RetroLoft/RadioFloppy/main/oled_font.h

/*
 * Classic 5x7 bitmap font, ASCII 0x20..0x7E. One byte per column, bit 0 =
 * top row (the SSD1306 page layout). Characters are drawn 6 pixels apart.
 */
#pragma once

#include <stdint.h>

#define OLED_FONT_FIRST     0x20
#define OLED_FONT_LAST      0x7e
#define OLED_FONT_WIDTH     5
#define OLED_FONT_HEIGHT    7

static const uint8_t oled_font5x7[][OLED_FONT_WIDTH] = {
    { 0x00, 0x00, 0x00, 0x00, 0x00 }, /* ' ' */  { 0x00, 0x00, 0x5f, 0x00, 0x00 }, /* ! */
    { 0x00, 0x07, 0x00, 0x07, 0x00 }, /* " */    { 0x14, 0x7f, 0x14, 0x7f, 0x14 }, /* # */
    { 0x24, 0x2a, 0x7f, 0x2a, 0x12 }, /* $ */    { 0x23, 0x13, 0x08, 0x64, 0x62 }, /* % */
    { 0x36, 0x49, 0x55, 0x22, 0x50 }, /* & */    { 0x00, 0x05, 0x03, 0x00, 0x00 }, /* ' */
    { 0x00, 0x1c, 0x22, 0x41, 0x00 }, /* ( */    { 0x00, 0x41, 0x22, 0x1c, 0x00 }, /* ) */
    { 0x08, 0x2a, 0x1c, 0x2a, 0x08 }, /* * */    { 0x08, 0x08, 0x3e, 0x08, 0x08 }, /* + */
    { 0x00, 0x50, 0x30, 0x00, 0x00 }, /* , */    { 0x08, 0x08, 0x08, 0x08, 0x08 }, /* - */
    { 0x00, 0x60, 0x60, 0x00, 0x00 }, /* . */    { 0x20, 0x10, 0x08, 0x04, 0x02 }, /* / */
    { 0x3e, 0x51, 0x49, 0x45, 0x3e }, /* 0 */    { 0x00, 0x42, 0x7f, 0x40, 0x00 }, /* 1 */
    { 0x42, 0x61, 0x51, 0x49, 0x46 }, /* 2 */    { 0x21, 0x41, 0x45, 0x4b, 0x31 }, /* 3 */
    { 0x18, 0x14, 0x12, 0x7f, 0x10 }, /* 4 */    { 0x27, 0x45, 0x45, 0x45, 0x39 }, /* 5 */
    { 0x3c, 0x4a, 0x49, 0x49, 0x30 }, /* 6 */    { 0x01, 0x71, 0x09, 0x05, 0x03 }, /* 7 */
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
    { 0x7c, 0x08, 0x04, 0x04, 0x78 }, /* n */    { 0x38, 0x44, 0x44, 0x44, 0x38 }, /* o */
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
};

_Static_assert(sizeof(oled_font5x7) / sizeof(oled_font5x7[0]) == OLED_FONT_LAST - OLED_FONT_FIRST + 1,
               "one glyph per character");
